unesjami/Gesture-Interaction-Robot-GIR-/schematic/GIR schematic.kicad_sch

## KiCad design schematic/GIR schematic.kicad_sch (2026-08-24)

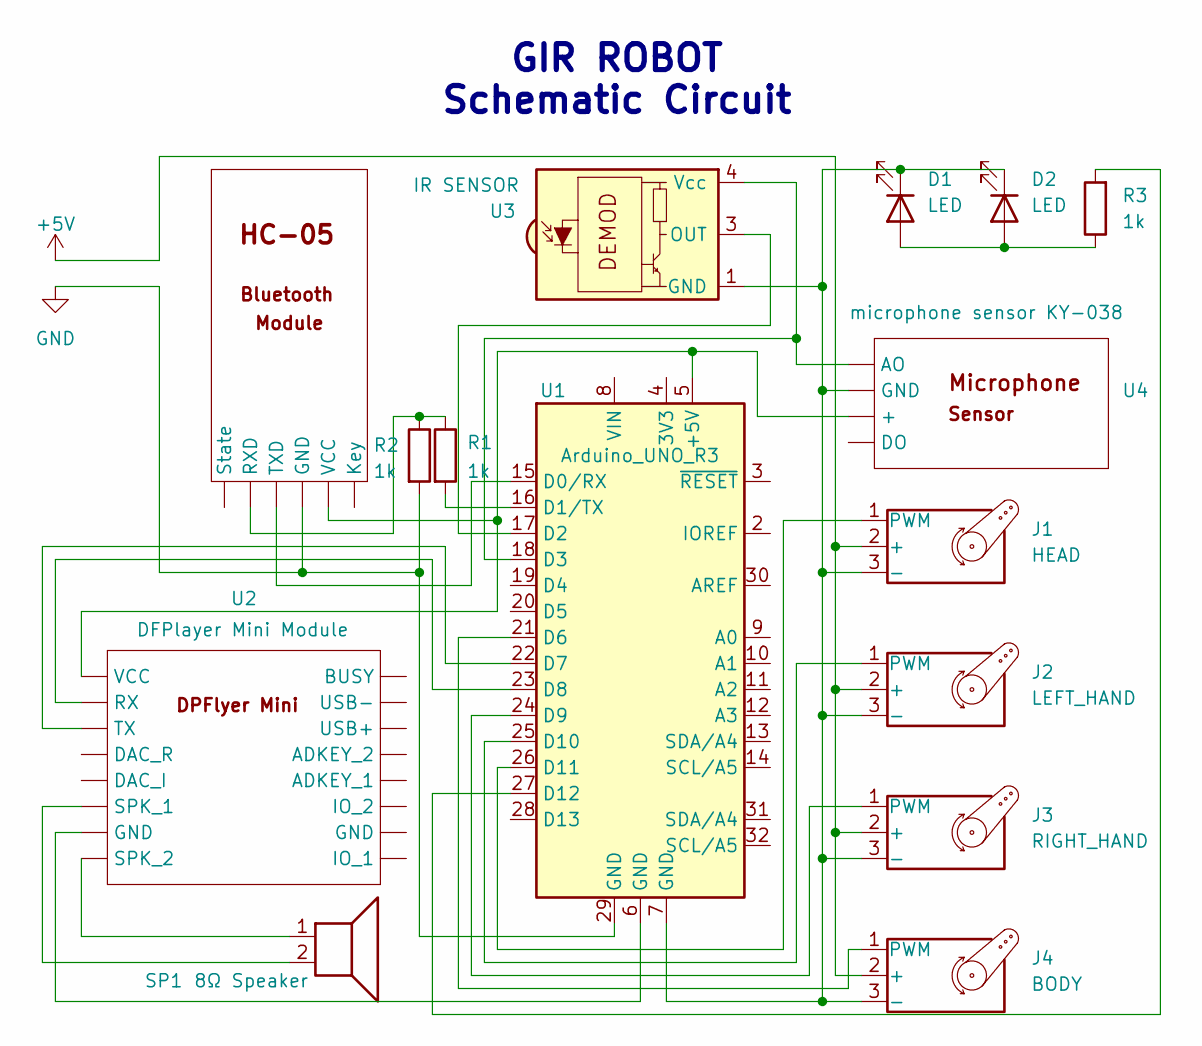
[picture p3: schematic GIR schematic.kicad_sch]

Parts:
D1, D2: LED
J1: HEAD
J2: LEFT_HAND
J3: RIGHT_HAND
J4: BODY
R1, R2, R3: 1k
SP1: 8Ω Speaker
U1: Arduino_UNO_R3
U2: DFPlayer Mini Module
U3: IR SENSOR; Everlight_IRM-H6xxT
U4: microphone sensor KY-038
U5: HC-05 Bluetooth Module

Connections:
+5V: J1.2 (+), J2.2 (+), J3.2 (+), J4.2 (+)
GND: R2.2, U1.29 (GND), U5.
unnamed: D1.1 (K), D2.1 (K), J1.3 (-), J2.3 (-), J3.3 (-), J4.3 (-), U1.7 (GND), U3.1 (GND), U3.2 (GND), U4.
unnamed: D1.2 (A), D2.2 (A), R3.1
unnamed: J1.1 (PWM), U1.26 (D11)
unnamed: J2.1 (PWM), U1.25 (D10)
unnamed: J3.1 (PWM), U1.24 (D9)
unnamed: J4.1 (PWM), U1.21 (D6)
unnamed: R1.1, R2.1, U5.
unnamed: R1.2, U1.16 (D1/TX)
unnamed: R3.2, U1.27 (D12)
unnamed: SP1.1, U2.
unnamed: SP1.2, U2.
unnamed: U1.5 (+5V), U2., U4., U5.
unnamed: U1.6 (GND), U2.
unnamed: U1.15 (D0/RX), U5.
unnamed: U1.17 (D2), U3.3 (OUT)
unnamed: U1.18 (D3), U3.4 (Vcc), U4.
unnamed: U1.22 (D7), U2.
unnamed: U1.23 (D8), U2.

Notes on the sheet:
GIR ROBOT Schematic Circuit
